Thaddeus-Maximus/dotclock/HEDC-F001/main/webpage_brotli.h

#ifndef HTML_CONTENT_BR_H
#define HTML_CONTENT_BR_H

#include <Arduino.h>

const unsigned char PROGMEM html_content_br[] = {
    0x1b, 0x75, 0x60, 0x11, 0x95, 0xac, 0x8c, 0x00, 0x3a, 0x12, 0xca, 0xb6, 0x9b, 0x34, 0xff, 0x95,
    0xc9, 0x8e, 0xfd, 0x65, 0x22, 0x13, 0x79, 0x9e, 0x98, 0xd2, 0x08, 0x49, 0x66, 0xff, 0xf7, 0x75,
    0xfa, 0xdf, 0xcd, 0xcf, 0x97, 0x18, 0x75, 0x74, 0xc3, 0x45, 0x88, 0xd5, 0x61, 0x45, 0xa6, 0x34,
    0x21, 0xdd, 0xa4, 0x99, 0x6f, 0xf0, 0x38, 0xbe, 0x06, 0x1b, 0xea, 0x13, 0x23, 0x38, 0x42, 0x59,
    0x4f, 0x08, 0xfa, 0x5f, 0x8b, 0xb5, 0x72, 0xe1, 0x2c, 0x82, 0x76, 0x43, 0xb2, 0x5e, 0x34, 0xf8,
    0xc1, 0x11, 0x17, 0x76, 0x19, 0xdc, 0x7d, 0x20, 0xc2, 0x53, 0x2e, 0xf7, 0xca, 0xde, 0xa1, 0x76,
    0xa9, 0x29, 0x80, 0xdb, 0x18, 0x87, 0xaa, 0x2f, 0x19, 0x42, 0x75, 0xa5, 0xfd, 0xcc, 0xff, 0x3f,
    0x5b, 0x96, 0x97, 0x81, 0x01, 0xa3, 0xcd, 0x2e, 0x48, 0x9c, 0x44, 0xcc, 0xd1, 0xc5, 0x4e, 0x42,
    0xf5, 0x87, 0xaa, 0x55, 0x75, 0x57, 0xeb, 0xdd, 0xe0, 0xbb, 0x99, 0x91, 0xb4, 0x34, 0xd2, 0x01,
    0xc0, 0xff, 0x55, 0xd5, 0x83, 0xda, 0x15, 0x2c, 0x8d, 0xb4, 0x7c, 0x00, 0x1c, 0x19, 0x5f, 0xee,
    0x30, 0x04, 0x0a, 0x42, 0x67, 0x91, 0x64, 0x4e, 0x2f, 0x74, 0x66, 0xab, 0xbb, 0xce, 0xde, 0x45,
    0x0a, 0xdf, 0xed, 0x31, 0x4a, 0x6b, 0x9f, 0xa4, 0x4f, 0xd2, 0xb4, 0x77, 0x9b, 0x19, 0x45, 0x44,
    0x54, 0x14, 0x74, 0x9e, 0x36, 0xf4, 0x84, 0x57, 0x73, 0x64, 0x71, 0x43, 0xca, 0x02, 0xc4, 0x0c,
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
    0xc0, 0x92, 0xdd, 0x29, 0x36, 0xaa, 0x4b, 0x55, 0xf3, 0x78, 0x89, 0xa4, 0x09, 0x4c, 0xf2, 0x76,
    0xa4, 0xd4, 0x4e, 0xcb, 0x27, 0x01, 0x32, 0x13, 0x57, 0x8a, 0x12, 0xf3, 0x23, 0x03, 0x4b, 0x77,
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
};

const unsigned int html_content_br_len = 5940;

#endif // HTML_CONTENT_BR_H
