Thaddeus-Maximus/dotclock/HEDC-F001/main/webpage_gzip.h

#ifndef HTML_CONTENT_GZ_H
#define HTML_CONTENT_GZ_H

#include <Arduino.h>

const unsigned char PROGMEM html_content_gz[] = {
    0x1f, 0x8b, 0x08, 0x00, 0x38, 0xff, 0x5b, 0x69, 0x02, 0xff, 0xed, 0x3d, 0x6b, 0x57, 0xdb, 0x48,
    0xb2, 0x9f, 0x77, 0x7e, 0x45, 0xc3, 0x24, 0x8c, 0x94, 0x08, 0xd9, 0x06, 0x32, 0x0f, 0x1b, 0x99,
    0x25, 0xe0, 0x4c, 0x32, 0x09, 0x8f, 0xc3, 0x23, 0x33, 0x7b, 0x59, 0x0e, 0x92, 0xad, 0x36, 0xd6,
    0x20, 0x4b, 0x1a, 0x49, 0x86, 0x30, 0xc2, 0xff, 0x7d, 0xab, 0xfa, 0x21, 0xb5, 0x64, 0xd9, 0x98,
    0x64, 0x33, 0x73, 0xee, 0xb9, 0x77, 0xf7, 0x2c, 0xb1, 0x5b, 0xdd, 0xd5, 0xd5, 0xf5, 0xae, 0xea,
    0x92, 0x77, 0x7b, 0xc5, 0x0d, 0x07, 0xe9, 0x7d, 0x44, 0xc9, 0x28, 0x1d, 0xfb, 0xdd, 0xed, 0xd4,
    0x4b, 0x7d, 0xda, 0xdd, 0x0b, 0x83, 0x34, 0x0e, 0x7d, 0x72, 0xec, 0x04, 0xd4, 0xdf, 0x6e, 0xf0,
    0xc1, 0xed, 0x31, 0x4d, 0x1d, 0x32, 0x80, 0x47, 0x34, 0x48, 0xad, 0xd5, 0x3b, 0xcf, 0x4d, 0x47,
    0x96, 0x4b, 0x6f, 0xbd, 0x01, 0x5d, 0x67, 0x5f, 0x0c, 0x2f, 0xf0, 0x52, 0xcf, 0xf1, 0xd7, 0x93,
    0x81, 0xe3, 0x53, 0xab, 0x65, 0x36, 0x57, 0x49, 0xe0, 0x8c, 0xa9, 0x75, 0xeb, 0xd1, 0xbb, 0x28,
    0x8c, 0xd3, 0xee, 0x76, 0x92, 0xde, 0x03, 0xa4, 0x6f, 0xef, 0x62, 0x27, 0x8a, 0x68, 0x9c, 0xa5,
    0xf4, 0x53, 0xba, 0xee, 0xf8, 0xde, 0x75, 0xd0, 0x1e, 0x00, 0x50, 0x1a, 0x77, 0xfa, 0xe1, 0xa7,
    0xf5, 0xc4, 0xfb, 0xd3, 0x0b, 0xae, 0xdb, 0xfd, 0x30, 0x76, 0x69, 0xbc, 0x0e, 0x23, 0xd3, 0x6f,
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
    0xa5, 0x7f, 0x8d, 0x70, 0x4a, 0xb0, 0xe6, 0x26, 0xa8, 0xc8, 0x0c, 0xed, 0xcc, 0xc1, 0x58, 0x62,
    0xc6, 0x79, 0xa0, 0x2a, 0xd5, 0x2b, 0x54, 0xaa, 0x6f, 0xc7, 0xc9, 0x75, 0x8d, 0xb0, 0x8d, 0x5a,
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
};

const unsigned int html_content_gz_len = 6845;

#endif // HTML_CONTENT_GZ_H
